razainno/Design-of-Optoelectronics-Based-Force-Sensor/Mechanical_Design/base22.JPG

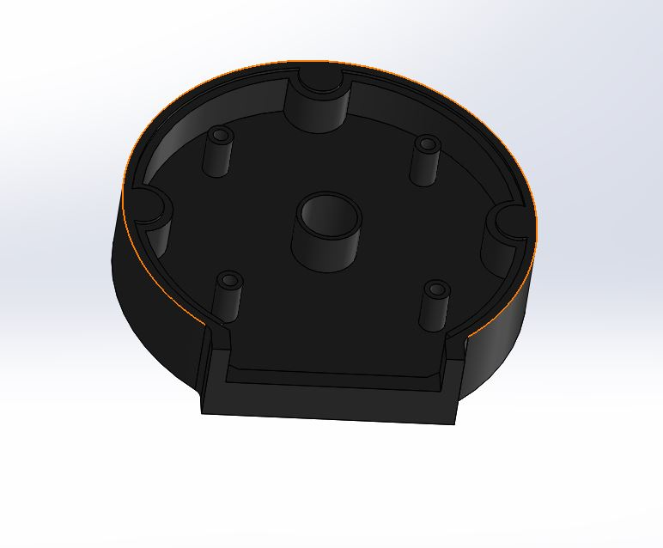
Mechanical_Design/base22.JPG
